SteveObert/KatanaUSB_Midi_controller/images/IMG_2592.JPG

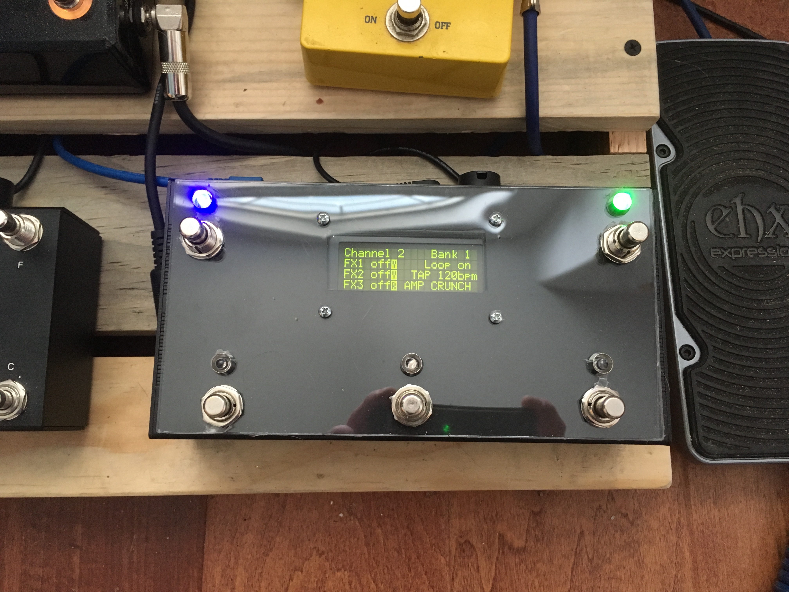
images/IMG_2592.JPG
